anthonydotmoe/68040pc/firmware/inc/bootparams_a68040pc.h

#pragma once

// 68040pc-specific boot information definitions

#define BP_A68040PC_VERSION     0x8000  /* model/version (uint32_t)   */
#define BP_A68040PC_DUARTBASE   0x8001  /* 68681 base addr (uint32_t) */
