anthonydotmoe/68040pc/firmware/inc/minmax.h

#pragma once

#define min(a,b)               \
    ({                         \
        typeof(a) __a = (a);   \
        typeof(b) __b = (b);   \
        __a < __b ? __a : __b; \
    })

#define max(a,b)               \
    ({                         \
        typeof(a) __a = (a);   \
        typeof(b) __b = (b);   \
        __a > __b ? __a : __b; \
    })
