anthonydotmoe/68040pc/firmware/src/c/ring_buffer.c

#include "ring_buffer.h"
#include "stringlib.h"

static struct ring_buffer _rb[RING_BUFFER_MAX];

/*
static void * memcpy(void *dest, const void *src, size_t len) {
    char *d = dest;
    const char *s = src;
    while (len--)
        *d++ = *s++;
    return dest;
}
*/

int ring_buffer_init(rbd_t *rbd, rb_attr_t *attr) {
    static int idx = 0;
    int err = -1;

    if ((idx < RING_BUFFER_MAX) && (rbd != NULL) && (attr != NULL)) {
        if ((attr->buffer != NULL) && (attr->s_elem > 0)) {
            /* Check that the size of the ring buffer is a power of 2 */
            if (((attr->n_elem - 1) & attr->n_elem) == 0) {
                /* Initialize the ring buffer internal variables */
                _rb[idx].head = 0;
                _rb[idx].tail = 0;
                _rb[idx].buf = attr->buffer;
                _rb[idx].s_elem = attr->s_elem;
                _rb[idx].n_elem = attr->n_elem;
                
                *rbd = idx++;
                err = 0;
            }
        }
    }
        
    return err;
}

static int _ring_buffer_full(struct ring_buffer *rb) {
    return ((rb->head - rb->tail) == rb->n_elem) ? 1 : 0;
}

static int _ring_buffer_empty(struct ring_buffer *rb) {
    return ((rb->head - rb->tail) == 0U) ? 1 : 0;
}

int ring_buffer_put(rbd_t rbd, const void *data) {
    int err = 0;

    if ((rbd < RING_BUFFER_MAX) && (_ring_buffer_full(&_rb[rbd]) == 0)) {
        const size_t offset = (_rb[rbd].head & (_rb[rbd].n_elem-1)) * _rb[rbd].s_elem;
        memcpy(&(_rb[rbd].buf[offset]), data, _rb[rbd].s_elem);
        _rb[rbd].head++;
    } else {
        err = -1;
    }
    
    return err;
}

int ring_buffer_get(rbd_t rbd, void *data) {
    int err = 0;

    if ((rbd < RING_BUFFER_MAX) && (_ring_buffer_empty(&_rb[rbd]) == 0)) {
        const size_t offset = (_rb[rbd].tail & (_rb[rbd].n_elem - 1)) * _rb[rbd].s_elem;
        memcpy(data, &(_rb[rbd].buf[offset]), _rb[rbd].s_elem);
        _rb[rbd].tail++;
    } else {
        err = -1;
    }
    
    return err;
}
