anthonydotmoe/68040pc/hdl/simpleboard/rtl/spixpress.v

////////////////////////////////////////////////////////////////////////////////
//
// Filename: 	spixpress.v
// {{{
// Project:	ICO Zip, iCE40 ZipCPU demonstration project
//
// Purpose:	This module is intended to be a low logic flash controller.
// 		It uses the 8'h03 read command from the flash, and so it
// 	cannot be used with a clock speed any greater than 50MHz.
//
//	Although this controller has no erase or program capability, it
//	includes a control port.  When using the control port, you should be
//	able to send arbitrary commands to the flash--but not read from the
//	flash during that time.
//
// Configuration:
//	In the interests of *LOW* logic, the controller has options for
//	OPT_CFG and OPT_PIPE.  If both are set to zero, the controller will be
//	in its lowest logic configuration.  That said, if you set OPT_CFG to
//	zero, you must also set i_cfg_stb to zero as well--lest you expect an
//	acknowledgement from a request made when i_cfg_stb is high.
//
// Actions:
// 	Control Port
// 	[31:9]	Unused bits, ignored on write, read as zero
// 	[8]	CS_n
// 			Can be activated via a write to the control port.
// 			This will render the memory addresses unreadable.
// 			Write a '1' to this value to return the memory to
// 			normal operation.
// 	[7:0]	BYTE-DATA
// 			Following a write to the control port where bit [8]
// 			is low, the controller will send bits [7:0] out the
// 			SPI port, top bit first.  Once accomplished, the
// 			control port may be read to see what values were
// 			read from the SPI port.  Those values will be stored
// 			in these same bits [7:0].
//
//	Memory
//		Returns the data from the address read
//
//		Requires that the CS_N setting within the control port be
//		deactivated, otherwise requests to read from memory
//		will simply return the control port register immediately
//		without doing anything.
//
// Creator:	Dan Gisselquist, Ph.D.
//		Gisselquist Technology, LLC
//
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
// This program is distributed in the hope that it will be useful, but WITHOUT
// ANY WARRANTY; without even the implied warranty of MERCHANTIBILITY or
// FITNESS FOR A PARTICULAR PURPOSE.  See the GNU General Public License
// for more details.
//
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
////////////////////////////////////////////////////////////////////////////////
//
//
`default_nettype	none
// }}}
module	spixpress(i_clk, i_reset,
        i_wb_cyc, i_wb_stb, i_wb_we, i_wb_addr, i_wb_data, i_wb_sel,
            o_wb_stall, o_wb_ack, o_wb_data,
        i_cfg_cyc, i_cfg_stb, i_cfg_we, i_cfg_data, i_cfg_sel,
            o_cfg_stall, o_cfg_ack, o_cfg_data,
        o_spi_cs_n, o_spi_sck, o_spi_mosi, i_spi_miso);
    //
    // OPT_PIPE allows successive, sequential, transactions to
    // incrementing addresses without requiring a new address to be sent.
    //
    // Random access performance:	65+64(N-1)
    // Performance when piped:	65+32(N-1)
    //
    parameter [0:0]	OPT_PIPE = 1'b1;
    //
    // OPT_CFG creates a configuration register that can be accessed through
    // i_cfg_stb when the core isn't busy.  Using this configuration
    // register, it is possible to send arbitrary commands to the flash,
    // and hence to erase or program the flash.  Since the access is
    // arbitrary, other flash features are supported as well such as
    // programming or reading the one-time-programmable memory or more.
    parameter [0:0]	OPT_CFG  = 1'b1;
    //
    parameter	AW = 24 - 2;
    parameter	DW = 32;
    //
    input	wire		i_clk, i_reset;
    //
    input	wire		i_wb_cyc, i_wb_stb, i_wb_we;
    input	wire [AW-1:0]	i_wb_addr;
    input	wire [DW-1:0]	i_wb_data;
    input	wire [DW/8-1:0]	i_wb_sel;
    output	wire		o_wb_stall, o_wb_ack;
    output	reg [DW-1:0]	o_wb_data;
    //
    input	wire		i_cfg_cyc, i_cfg_stb, i_cfg_we;
    input	wire [DW-1:0]	i_cfg_data;
    input	wire [DW/8-1:0]	i_cfg_sel;
    output	wire		o_cfg_stall, o_cfg_ack;
    output	wire [DW-1:0]	o_cfg_data;
    //
    output	reg		o_spi_cs_n, o_spi_sck, o_spi_mosi;
    input	wire		i_spi_miso;
    //
    //

    //
    // Arbitrated bus registers and inputs
    //
    wire		bus_cyc, bus_stb, bus_we, ign_wb_err, ign_cfg_err;
    wire	[AW-1:0] bus_addr;
    wire [DW-1:0]	bus_data;
    wire [DW/8-1:0]	bus_sel;
    reg		bus_stall, bus_ack;
    wire		cfg_bus_stb, mem_bus_stb;

    generate if (OPT_CFG)
    begin : ARBITER
        wire	cfg_bus_grant;
        //
        // Memory vs Configuration bus arbiter
        //
        wbarbiter #(
            // {{{
            .DW(DW), .AW(AW+1), .SCHEME("PRIORITY"),
`ifdef	FORMAL
            .F_MAX_STALL(0), .F_MAX_ACK_DELAY(0)
`endif
            // }}}
        ) arbiter(
            // {{{
            i_clk, i_reset,
            i_wb_cyc, i_wb_stb, i_wb_we, { 1'b0, i_wb_addr },
                i_wb_data, i_wb_sel,
                o_wb_stall, o_wb_ack, ign_wb_err,
            i_cfg_cyc, i_cfg_stb, i_cfg_we, { 1'b1, i_wb_addr },
                i_cfg_data, i_cfg_sel,
                o_cfg_stall, o_cfg_ack, ign_cfg_err,
            bus_cyc, bus_stb, bus_we, { cfg_bus_grant, bus_addr },
                bus_data, bus_sel, bus_stall, bus_ack, 1'b0
            // }}}
        );

        assign	cfg_bus_stb = bus_stb &&  cfg_bus_grant;
        assign	mem_bus_stb = bus_stb && !cfg_bus_grant;
        assign	o_cfg_data  = o_wb_data;

        // Verilator lint_off UNUSED
        wire	unused;
        assign	unused = &{ 1'b0, bus_data, bus_addr,
                    ign_cfg_err, ign_wb_err };
        // Verilator lint_on UNUSED
    end else begin
        assign	bus_cyc    = i_wb_cyc;
        assign	bus_stb    = i_wb_stb;
        assign	bus_we     = i_wb_we;
        assign	bus_addr   = i_wb_addr;
        assign	bus_data   = i_wb_data;
        assign	bus_sel    = i_wb_sel;
        //
        assign	o_wb_ack   = bus_ack;
        assign	o_wb_stall = bus_stall;

        assign	mem_bus_stb = bus_stb;
        assign	cfg_bus_stb = 0;
        assign	o_cfg_ack   = i_cfg_stb;
        assign	o_cfg_stall = 0;
        assign	o_cfg_data  = 0;
    end endgenerate

    reg		cfg_user_mode;
    reg	[32:0]	wdata_pipe;
    reg	[6:0]	ack_delay;
    reg		actual_sck;

    wire	[AW-1:0]	next_addr;

    wire	bus_request, next_request, user_request;

    assign	bus_request  = (mem_bus_stb)&&(!bus_stall)
                    &&(!bus_we)&&(!bus_stall);
    assign	next_request = (OPT_PIPE)&&(mem_bus_stb)&&(!bus_we)
                    &&(!cfg_user_mode)
                    &&(i_wb_addr == next_addr);
    assign	user_request = (OPT_CFG)&&(cfg_bus_stb)&&(!bus_stall)
                    &&(bus_we)&&(!bus_data[8]);


    //
    // State control
    //
    // The state control is nominally the number of clocks to wait until
    // the current operation finishes.  Once ack_delay transitions to 0,
    // the operation is finished and bus_ack should be high.
    initial	ack_delay = 0;
    always @(posedge i_clk)
    if ((i_reset)||(!bus_cyc))
        ack_delay <= 0;
    else if (bus_request)
        ack_delay <= ((o_spi_cs_n)||(!OPT_PIPE)) ? 7'd65 : 7'd32;
    else if (user_request)
        ack_delay <= 7'd9;
    else if (ack_delay != 0)
        ack_delay <= ack_delay - 1'b1;

    //
    // MOSI
    //
    // wdata_pipe is a long shift register, containing values that need
    // to be sent to the SPI port for our current transaction.  The
    // basic transaction requires sending a 8'h03 (read) command, followed
    // by a 24-bit address.
    //
    // For purposes of logic minimization, setting wdata_pipe has been
    // broken up into two sections, but it basically follows a couple
    // of models:
    //
    // 1. Upon any flash read request, request a read from the 24-bit
    //	address formed from i_wb_addr[AW-1:0] and 2'b00--since we are
    //	only doing aligned transactions.
    //
    //	wdata_pipe <= { 1'b0, 8'h03, i_wb_addr[AW-1:0], 2'b00 };
    //
    // 2. Upon any configuration port write, set the data based upon the
    //	desired 8-bit command contained in i_wb_data
    //
    //	wdata_pipe <= { 1'b0, i_wb_data[7:0], 24'bz };
    //
    // 3. During any operation, shift the pipe up/left one bit per clock,
    //	backfilling with 1'bz nominally, but 1'b0 in actuality
    //
    // 4. If the interface is idle, wdata_pipe is a don't care.
    //
    // 
    initial	wdata_pipe = 0;
    always @(posedge i_clk)
    if (!bus_stall)
    begin
        // On any read request, this sets the address to be read.
        //
        // On a configuration write request, or if the bus is idle,
        // these bits are don't cares so we can optimize them a bit
        wdata_pipe[23:0] <= 0;
        wdata_pipe[(AW+1):2] <= bus_addr[AW-1:0];
    end else
        // While in operation, just shift left one bit at a time
        wdata_pipe[23:0] <= { wdata_pipe[22:0], 1'b0 };

    always @(posedge i_clk)
    if (((!OPT_CFG)||(mem_bus_stb))&&(!bus_stall)) // (bus_request)
        // Request to read from the flash
        wdata_pipe[32:24] <= { 1'b0, 8'h03 };
    else if ((OPT_CFG)&&(!bus_stall)) // (user_request)
        // Request to send special data to the flash
        wdata_pipe[32:24] <= { 1'b0, i_cfg_data[7:0] };
    else
        // Otherwise just shift the register left
        wdata_pipe[32:24] <= { wdata_pipe[31:23] };

    // The outgoing bit to the flash is simply given by the top bit of
    // this wdata_pipe shift register.
    always @(*)
        o_spi_mosi = wdata_pipe[32];

    //
    // WB-ACK
    //
    initial	bus_ack = 0;
    always @(posedge i_clk)
    if (i_reset)
        // Clear any acknowledgment on reset
        bus_ack <= 0;
    else if (ack_delay == 1)
        // Acknowledge the end of any operation, whether from the
        // configuration port or from reading the memory
        bus_ack <= (bus_cyc);
    else if ((bus_stb)&&(!bus_stall)&&(!bus_request))
        // Immediately acknowledge any write to the memory address
        // space, or any read/write while the configuration port is
        // active.
        bus_ack <= 1'b1;
    else if ((cfg_bus_stb)&&(!bus_stall)&&(!user_request))
        // Immediately acknowledge any read from the configuration
        // port.  No action is required.
        bus_ack <= 1'b1;
    else
        // In all other cases, leave the acknowledgment line low.
        bus_ack <= 0;

    //
    // CFG user mode (i.e. override mode)
    //
    // If we are in the configuration/user mode, the CS line will be held
    // low artificially.  This allows us to send multiply byte commands
    // over a series of configuration writes.
    //
    initial	cfg_user_mode = 0;
    always @(posedge i_clk)
    if (i_reset)
        cfg_user_mode <= 0;
    else if ((OPT_CFG)&&(cfg_bus_stb)&&(!bus_stall)&&(bus_we))
        cfg_user_mode <= !i_cfg_data[8];

    //
    // Actual_sck (SCK, but delayed by one)
    //
    // This is the SCK signal the hardware sees
    initial	actual_sck = 1'b0;
    always @(posedge i_clk)
    if ((i_reset)||(!bus_cyc))
        actual_sck <= 1'b0;
    else
        // Our SCK signal is delayed by one clock from our request
        // to transmit the SCK.  We'll create a delayed copy of it
        // here so we can tell what the actual one is doing.
        actual_sck <= o_spi_sck;

    //
    // Outgoing WB-Data
    //
    always @(posedge i_clk)
    begin
        if (actual_sck)
        begin
            if (cfg_user_mode)
                o_wb_data <= { 19'h0, 1'b1, 4'h0, o_wb_data[6:0], i_spi_miso };
            else
                o_wb_data <= { o_wb_data[30:0], i_spi_miso };
        end

        if (cfg_user_mode)
            o_wb_data[31:8] <= { 19'h0, 1'b1, 4'h0 };
    end

    //
    // CSN
    //
    // This is the negative logic chip select.
    //
    initial	o_spi_cs_n = 1'b1;
    always @(posedge i_clk)
    if (i_reset)
        // Idle on reset
        o_spi_cs_n <= 1'b1;
    else if ((!bus_cyc)&&(!cfg_user_mode))
        // Following any aborted transaction, or any time we
        // leave the configuration mode, return to idle.
        o_spi_cs_n <= 1'b1;
    else if (bus_request)
        // On any bus read request, select the device to initiate a
        // transaction.
        o_spi_cs_n <= 1'b0;
    else if ((OPT_CFG)&&(cfg_bus_stb)&&(!bus_stall)&&(bus_we))
        // Similarly, on any write to the configuration port, begin
        // an 8-bit transfer.
        o_spi_cs_n <= bus_data[8];
    else if (cfg_user_mode)
        // Even if the transfer is complete, while we are in
        // configuration mode hold the CS line active (low)
        o_spi_cs_n <= 1'b0;
    else if ((ack_delay == 1)&&(!cfg_user_mode))
        // In all other cases, a transaction should end on the clock
        // following ack_delay == 1, so end it here.
        o_spi_cs_n <= 1'b1;

    //
    // SCK
    //
    initial	o_spi_sck = 1'b0;
    always @(posedge i_clk)
    if (i_reset)
        o_spi_sck <= 1'b0;
    else if ((bus_request)||(user_request))
        // Start clocking following any memory read or configuration
        // port write request
        o_spi_sck <= 1'b1;
    else if ((bus_cyc)&&(ack_delay > 2)) // Bus abort check
        // As long as CYC stays high, continue the request
        o_spi_sck <= 1'b1;
    else if ((next_request)&&(ack_delay == 2))
        // On any pipelined read request, keep the clock running
        o_spi_sck <= 1'b1;
    else
        // Otherwise, shut it down
        o_spi_sck <= 1'b0;

    //
    // WB-stall
    //
    // The WB interface needs to stall any time we are busy calculating
    // an answer, as this core can only process one request at a time.
    initial	bus_stall = 1'b0;
    always @(posedge i_clk)
    if ((i_reset)||(!bus_cyc))
        // Release the stall line on a reset, or bus abort
        bus_stall <= 1'b0;
    else if ((bus_request)||(user_request))
        // On any request for a flash transaction, immediately start
        // stalling the bus
        bus_stall <= 1'b1;
    else if ((next_request)&&(ack_delay == 2))
        // This one is tricky.  If there's a request for a subsequent
        // read transaction, we'll need to lower the stall line in
        // order to accept it.  This depends upon the bus request
        // remaining stable for another clock period.
        bus_stall <= 1'b0;
    else
        bus_stall <= (ack_delay > 1);

    generate if (OPT_PIPE)
    begin
        reg	[AW-1:0]	r_next_addr;
        always @(posedge i_clk)
        if (!bus_stall)
            r_next_addr <= i_wb_addr + 1'b1;

        assign	next_addr = r_next_addr;

    end else begin

        assign next_addr = 0;

    end endgenerate

    // verilator lint_off UNUSED
    wire	unused;
    assign	unused = &{ 1'b0, bus_data[DW-1:9], bus_sel };
    // verilator lint_on  UNUSED

////////////////////////////////////////////////////////////////////////////////
////////////////////////////////////////////////////////////////////////////////
//
// Formal properties section
//
////////////////////////////////////////////////////////////////////////////////
////////////////////////////////////////////////////////////////////////////////
`ifdef	FORMAL
    parameter	[0:0]	F_OPT_COVER = 1'b0;

    reg	f_past_valid;

    initial	f_past_valid = 1'b0;
    always @(posedge i_clk)
        f_past_valid <= 1'b1;

    ////////
    //
    // Reset logic
    //
    ////////
    always @(*)
    if (!f_past_valid)
        assume(i_reset);
`ifndef	VERIFIC
    initial	assume(i_reset);
`endif

    always @(posedge i_clk)
    if ((!f_past_valid)||($past(i_reset)))
    begin
        assert(o_spi_cs_n == 1'b1);
        assert(o_spi_sck  == 1'b0);
        //
        assert(ack_delay    ==  0);
        assert(cfg_user_mode == 0);
        assert(bus_stall == 1'b0);
        assert(bus_ack   == 1'b0);
    end

    localparam	F_LGDEPTH = 7;
    wire	[F_LGDEPTH-1:0]	f_nreqs, f_nacks, f_outstanding;

    fwb_slave #( .AW(22), .F_MAX_STALL(7'd66), .F_MAX_ACK_DELAY(7'd66),
            .F_LGDEPTH(F_LGDEPTH),
            .F_MAX_REQUESTS((OPT_PIPE) ? 0 : 1'b1),
            .F_OPT_MINCLOCK_DELAY(1'b1)
        ) slavei(i_clk, (i_reset),
        bus_cyc, (bus_stb), bus_we,
            bus_addr, bus_data, 4'hf,
            bus_ack, bus_stall, bus_data, 1'b0,
            f_nreqs, f_nacks, f_outstanding);

    always @(*)
    if (OPT_PIPE)
        assert(f_outstanding <= 2);
    else
        assert(f_outstanding <= 1);

    always @(posedge i_clk)
    if (ack_delay == 0)
        assert((bus_ack)||(f_outstanding == 0));


    always @(posedge i_clk)
    if ((f_past_valid)&&(!i_reset)&&(bus_cyc))
    begin
        if (((!OPT_PIPE)||($past(o_spi_cs_n)))
            &&($past(bus_stb))&&(!$past(bus_stall))&&(bus_cyc))
            assert(f_outstanding == 1);
        if (ack_delay > 0)
            assert((bus_ack)||(f_outstanding == 1));
    end

    always @(posedge i_clk)
    if ((f_past_valid)&&(bus_ack)&&($past(bus_ack)))
        assert(f_outstanding <= 1);

    always @(posedge i_clk)
    if (f_outstanding == 2)
        assert((OPT_PIPE)&&(bus_ack)&&(!o_spi_cs_n)&&(o_spi_sck)
            &&(ack_delay==7'd32));

    always @(posedge i_clk)
    if ((f_past_valid)&&($past(bus_stb))&&(!$past(bus_stall)))
    begin
        if ((bus_cyc)&&(!i_reset)
                &&(!$past(user_request))&&(!$past(bus_request)))
            assert((bus_ack)&&(f_outstanding == 1));
    end

    //
    // SPI protocol assertions
    //
    always @(*)
    if (o_spi_cs_n)
        assert(!o_spi_sck);

    always @(*)
        assert((o_spi_sck||actual_sck) == (ack_delay > 0));

    always @(*)
    if (ack_delay == 0)
        assert(!bus_stall);
    else if (ack_delay > 1)
        assert(bus_stall);
    else if ((!OPT_PIPE)&&(ack_delay == 1))
        assert(bus_stall);

    always @(*)
        assert(ack_delay <= 7'd65);

//	always @(*)
//	if (cfg_user_mode)
//		assert(ack_delay <= 7'd9);

    always @(*)
        assert(o_spi_cs_n != ((cfg_user_mode)||(ack_delay > 0)));

    generate if (F_OPT_COVER)
    begin

        always @(posedge i_clk)
            cover(bus_ack&&(!$past(bus_request))
                &&(!$past(user_request)));

        reg	f_pending_user_request, f_pending_bus_request;

        initial	f_pending_user_request = 1'b0;
        always @(posedge i_clk)
        if ((i_reset)||(!bus_cyc))
            f_pending_user_request <= 1'b0;
        else if (user_request)
            f_pending_user_request <= 1'b1;
        else if (bus_ack)
            f_pending_user_request <= 1'b0;

        initial	f_pending_bus_request = 1'b0;
        always @(posedge i_clk)
        if ((i_reset)||(!bus_cyc))
            f_pending_bus_request <= 1'b0;
        else if (bus_request)
            f_pending_bus_request <= 1'b1;
        else if (bus_ack)
            f_pending_bus_request <= 1'b0;

        always @(posedge i_clk)
            cover((bus_ack)&&(f_pending_user_request));

        always @(posedge i_clk)
            cover((bus_ack)&&(f_pending_bus_request));

        if (OPT_PIPE)
        begin

            always @(posedge i_clk)
                cover((f_pending_bus_request)
                    &&(ack_delay == 7'h1)
                    &&(bus_request)&&(o_spi_sck));
            always @(posedge i_clk)
                cover((next_request)&&(f_pending_bus_request)&&(ack_delay == 7'h2));
        end

    end endgenerate

`endif
`ifdef	VERIFIC
    reg	[AW-1:0]	f_last_addr, f_next_addr;

    always @(posedge i_clk)
    if (bus_request)
        f_last_addr <= bus_addr[AW-1:0];

    always @(*)
        f_next_addr <= f_last_addr + 1'b1;

    // Writes are immediately returned
    assert property (@(posedge i_clk)
        disable iff ((i_reset)||(!bus_cyc))
        (bus_stb)&&(!bus_stall)
                &&(!user_request)&&(!bus_request)
        |=> (bus_ack)&&(!bus_stall));

    assert property (@(posedge i_clk)
        (mem_bus_stb)&&(!bus_stall)&&(!o_spi_cs_n)&&(!bus_we)
            // &&(!cfg_user_mode)
        |-> (OPT_PIPE)&&(bus_addr[AW-1:0] == f_next_addr)
        );

    sequence READ_COMMAND;
        // Send command 8'h03
        (f_last_addr == $past(i_wb_addr))
                &&(!o_spi_cs_n)&&(o_spi_sck)&&(!o_spi_mosi)
                &&(!actual_sck)
        ##1 ( ((f_last_addr == $past(f_last_addr))
            &&(!o_spi_cs_n)&&(o_spi_sck)&&(actual_sck)) throughout
                (!o_spi_mosi)&&(ack_delay==7'd64)&&(actual_sck)
                ##1 (!o_spi_mosi)&&(ack_delay==7'd63)
                ##1 (!o_spi_mosi)&&(ack_delay==7'd62)
                ##1 (!o_spi_mosi)&&(ack_delay==7'd61)
                ##1 (!o_spi_mosi)&&(ack_delay==7'd60)
                ##1 (!o_spi_mosi)&&(ack_delay==7'd59)
                ##1 ( o_spi_mosi)&&(ack_delay==7'd58)
                ##1 ( o_spi_mosi)&&(ack_delay==7'd57));
    endsequence

    sequence	SEND_ADDRESS;
        (((f_last_addr == $past(f_last_addr))&&(!o_spi_cs_n)&&(o_spi_sck)
            &&(actual_sck))
        throughout
            (o_spi_mosi == f_last_addr[21])&&(ack_delay==7'd56)
            ##1 (o_spi_mosi == f_last_addr[20])&&(ack_delay==7'd55)
            ##1 (o_spi_mosi == f_last_addr[19])&&(ack_delay==7'd54)
            ##1 (o_spi_mosi == f_last_addr[18])&&(ack_delay==7'd53)
            ##1 (o_spi_mosi == f_last_addr[17])&&(ack_delay==7'd52)
            ##1 (o_spi_mosi == f_last_addr[16])&&(ack_delay==7'd51)
            ##1 (o_spi_mosi == f_last_addr[15])&&(ack_delay==7'd50)
            ##1 (o_spi_mosi == f_last_addr[14])&&(ack_delay==7'd49)
            ##1 (o_spi_mosi == f_last_addr[13])&&(ack_delay==7'd48)
            ##1 (o_spi_mosi == f_last_addr[12])&&(ack_delay==7'd47)
            ##1 (o_spi_mosi == f_last_addr[11])&&(ack_delay==7'd46)
            ##1 (o_spi_mosi == f_last_addr[10])&&(ack_delay==7'd45)
            ##1 (o_spi_mosi == f_last_addr[ 9])&&(ack_delay==7'd44)
            ##1 (o_spi_mosi == f_last_addr[ 8])&&(ack_delay==7'd43)
            ##1 (o_spi_mosi == f_last_addr[ 7])&&(ack_delay==7'd42)
            ##1 (o_spi_mosi == f_last_addr[ 6])&&(ack_delay==7'd41)
            ##1 (o_spi_mosi == f_last_addr[ 5])&&(ack_delay==7'd40)
            ##1 (o_spi_mosi == f_last_addr[ 4])&&(ack_delay==7'd39)
            ##1 (o_spi_mosi == f_last_addr[ 3])&&(ack_delay==7'd38)
            ##1 (o_spi_mosi == f_last_addr[ 2])&&(ack_delay==7'd37)
            ##1 (o_spi_mosi == f_last_addr[ 1])&&(ack_delay==7'd36)
            ##1 (o_spi_mosi == f_last_addr[ 0])&&(ack_delay==7'd35)
            ##1 (o_spi_mosi == 1'b0)&&(ack_delay==7'd34)
            ##1 (o_spi_mosi == 1'b0)&&(ack_delay==7'd33));
    endsequence

    sequence	READ_DATA;
        (((o_wb_stall)&&(!o_spi_cs_n)&&(o_spi_sck)
            &&(o_wb_data == $past({o_wb_data[30:0], i_spi_miso})))
        throughout
        (ack_delay <= 7'd32)&&(ack_delay >= 7'd25) [*8]
        ##1 (ack_delay <= 7'd24)&&(ack_delay >= 7'd17) [*8]
        ##1 (ack_delay <= 7'd16)&&(ack_delay >=  7'd9) [*8]
        ##1 (ack_delay <=  7'd8)&&(ack_delay >=  7'd2) [*7])
        ##1 ((!o_spi_cs_n)&&(actual_sck)&&(ack_delay == 7'd1)
            &&(((OPT_PIPE)&&(i_wb_stb)&&(!i_wb_we)&&(o_spi_sck))
                ||((o_wb_stall)&&(!o_spi_sck)))
            &&(o_wb_data == $past({o_wb_data[30:0], i_spi_miso})))
        ##1 (o_wb_ack)
            &&(o_wb_data == $past({o_wb_data[30:0], i_spi_miso}))
            &&((OPT_PIPE)||((o_spi_cs_n)
                    &&(!o_spi_sck)&&(!actual_sck)));
    endsequence

    assert property (@(posedge i_clk)
        disable iff ((i_reset)||(!i_wb_cyc))
        (i_wb_stb)&&(!o_wb_stall)&&(!i_wb_we)&&(o_spi_cs_n)
            &&(!cfg_user_mode)
        // Send command 8'h03
        |=> READ_COMMAND
        ##1 ((f_last_addr == $past(f_last_addr)) throughout
                SEND_ADDRESS)
        ##1 READ_DATA);


    //////////////
    //
    // The known data/address contract
    //
    /////////////
    (* anyconst *) wire	[31:0]	f_data;

    sequence	DATA_BYTE(local input [7:0] B);
        (i_spi_miso == B[7])
        ##1 (i_spi_miso == B[6])
        ##1 (i_spi_miso == B[5])
        ##1 (i_spi_miso == B[4])
        ##1 (i_spi_miso == B[3])
        ##1 (i_spi_miso == B[2])
        ##1 (i_spi_miso == B[1])
        ##1 (i_spi_miso == B[0]);
    endsequence

    sequence	THIS_DATA;
            DATA_BYTE(f_data[31:24])
            ##1 DATA_BYTE(f_data[23:16])
            ##1 DATA_BYTE(f_data[15: 8])
            ##1 DATA_BYTE(f_data[ 7: 0]);
    endsequence

    assert property (@(posedge i_clk)
        (THIS_DATA and ((!i_reset)&&(i_wb_cyc)
            throughout
        ((ack_delay == 7'd32)
            ##1 (ack_delay == $past(ack_delay)-1) [*31])))
        |=> (o_wb_ack)&&(o_wb_data == f_data));

    generate if (OPT_CFG)
    begin
        // Now for configuration writes
        assert property (@(posedge i_clk)
            disable iff ((i_reset)||(!i_wb_cyc))
            ((i_cfg_stb)&&(!o_wb_stall)&&(i_wb_we)&&(i_wb_data[8]))
            |=> ((!cfg_user_mode)&&(o_spi_cs_n)&&(!o_spi_sck))
                &&(o_wb_ack)&&(!o_wb_stall));

        reg	[7:0]	f_wr_data;
        always @(posedge i_clk)
        if (user_request)
            f_wr_data <= i_wb_data[7:0];

        assert property (@(posedge i_clk)
            disable iff ((i_reset)||(!i_wb_cyc))
            ((i_cfg_stb)&&(!o_wb_stall)&&(i_wb_we)&&(!i_wb_data[8]))
            |=> (((cfg_user_mode)&&(!o_spi_cs_n)&&(o_spi_sck)
                &&(o_wb_stall)) throughout
                (!o_spi_mosi)&&(ack_delay==7'd9)
                ##1 (o_spi_mosi == f_wr_data[7])
                            &&(ack_delay==7'd8)
                ##1 (o_spi_mosi == f_wr_data[6])
                            &&(ack_delay==7'd7)
                ##1 (o_spi_mosi == f_wr_data[5])
                            &&(ack_delay==7'd6)
                ##1 (o_spi_mosi == f_wr_data[4])
                            &&(ack_delay==7'd5)
                ##1 (o_spi_mosi == f_wr_data[3])
                            &&(ack_delay==7'd4)
                ##1 (o_spi_mosi == f_wr_data[2])
                            &&(ack_delay==7'd3)
                ##1 (o_spi_mosi == f_wr_data[1])
                            &&(ack_delay==7'd2))
            ##1 ((cfg_user_mode)&&(!o_spi_cs_n)&&(!o_spi_sck)
                &&(actual_sck)&&(o_wb_stall)
                &&(o_spi_mosi == f_wr_data[0])
                            &&(ack_delay==7'd1))
            ##1 (o_wb_ack)&&(!o_wb_stall)&&(cfg_user_mode)
                &&(!o_spi_sck)&&(!actual_sck)&&(!o_wb_stall));

        // And then configuration reads.  First the write needs to
        // charge the o_wb_data buffer
        assert property (@(posedge i_clk)
            disable iff ((i_reset)||(!i_wb_cyc))
            ((i_cfg_stb)&&(!o_wb_stall)&&(i_wb_we)&&(!i_wb_data[8]))
            ##2 DATA_BYTE(f_data[7:0])
            |=> (o_wb_ack)&&(o_wb_data == { 24'h10,
                $past(i_spi_miso,8), $past(i_spi_miso,7),
                $past(i_spi_miso,6), $past(i_spi_miso,5),
                $past(i_spi_miso,4), $past(i_spi_miso,3),
                $past(i_spi_miso,2), $past(i_spi_miso,1)
                })
                &&(cfg_user_mode)&&(!o_wb_stall));

        // Then it needs to stay constant until another SPI
        // command
        assert property (@(posedge i_clk)
            disable iff (i_reset)
            ($past(!o_spi_sck))&&(!o_spi_sck)&&(cfg_user_mode)
            |=> $stable(o_wb_data)&&(o_wb_data[31:8]==5'h10));

    end endgenerate
`endif
endmodule
// Usage on an iCE40
// 		NoCfg	NoPipe	P/NCfg	Piped
// Cells	133	168	226	259
// SB_CARRY	 16	 16	 36	 36
// SB_DFF	 10	 32	 10	 32
// SB_DFFE	 33	 10	 55	 32
// SB_DFFESR	  7	  9	  7	  9
// SB_DFFSR	 12	 12	 12	 12
// SB_DFFSS	  2	  2	  2	  2
// SB_LUT4	 53	 87	104	136
//
